TheSoundCoder/GameChatBalancer/AudioControl/Resources/Chat.png

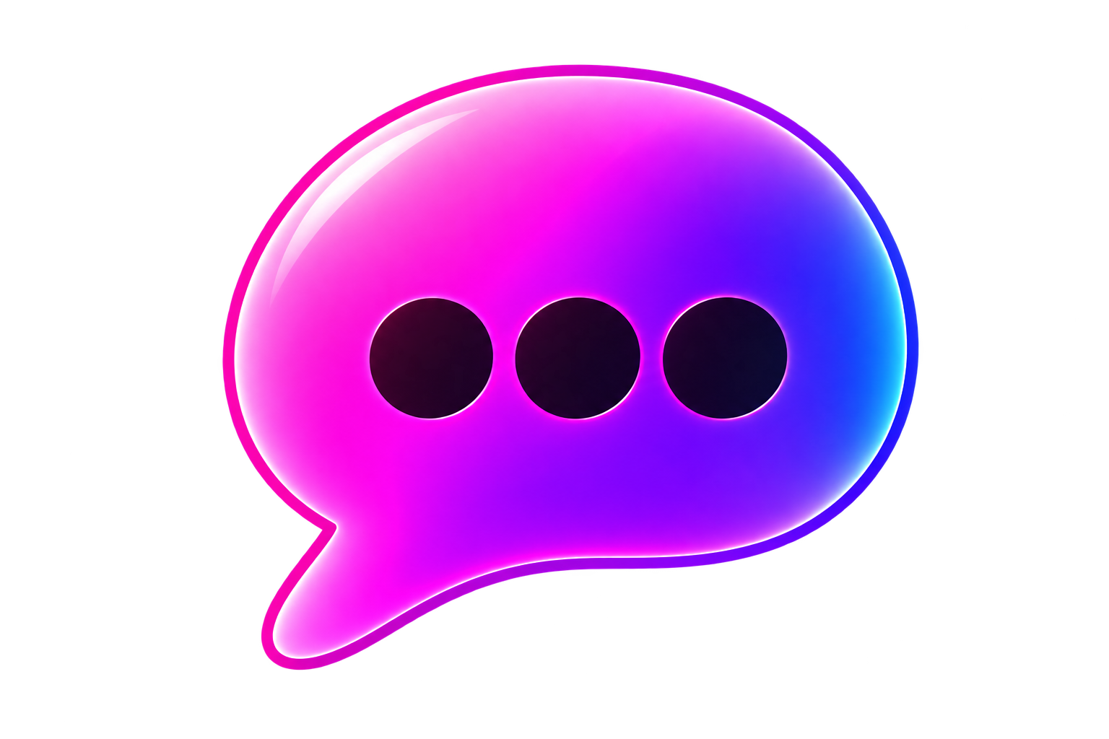
AudioControl/Resources/Chat.png
