TheSoundCoder/GameChatBalancer/AudioControl/Resources/Gamepad.png

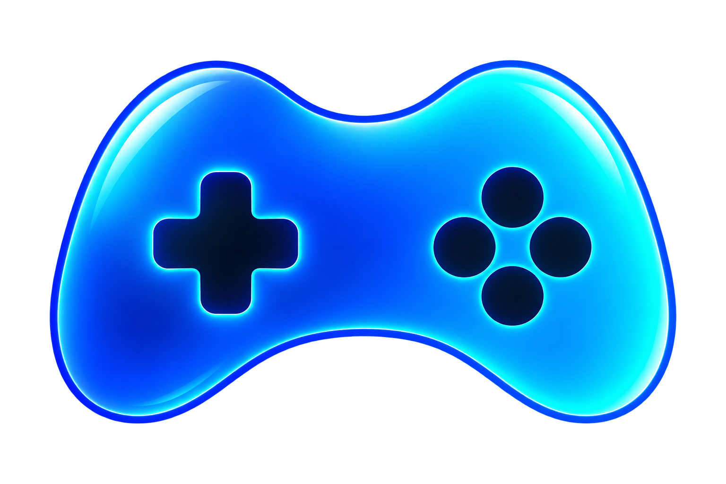
AudioControl/Resources/Gamepad.png
