TheSoundCoder/GameChatBalancer/AudioControl/Resources/ico_game2.png

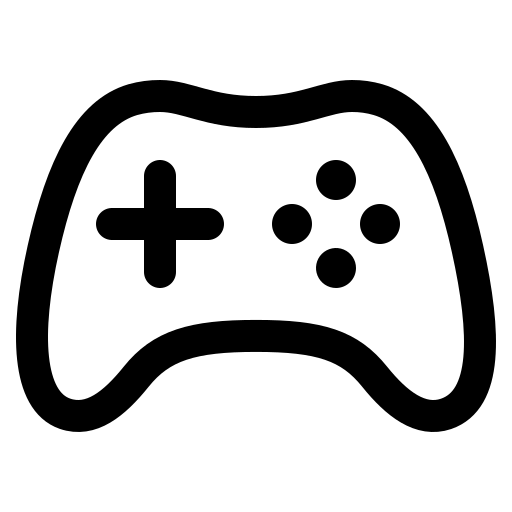
AudioControl/Resources/ico_game2.png
