TheSoundCoder/GameChatBalancer/AudioControl/Resources/Title_Background.png

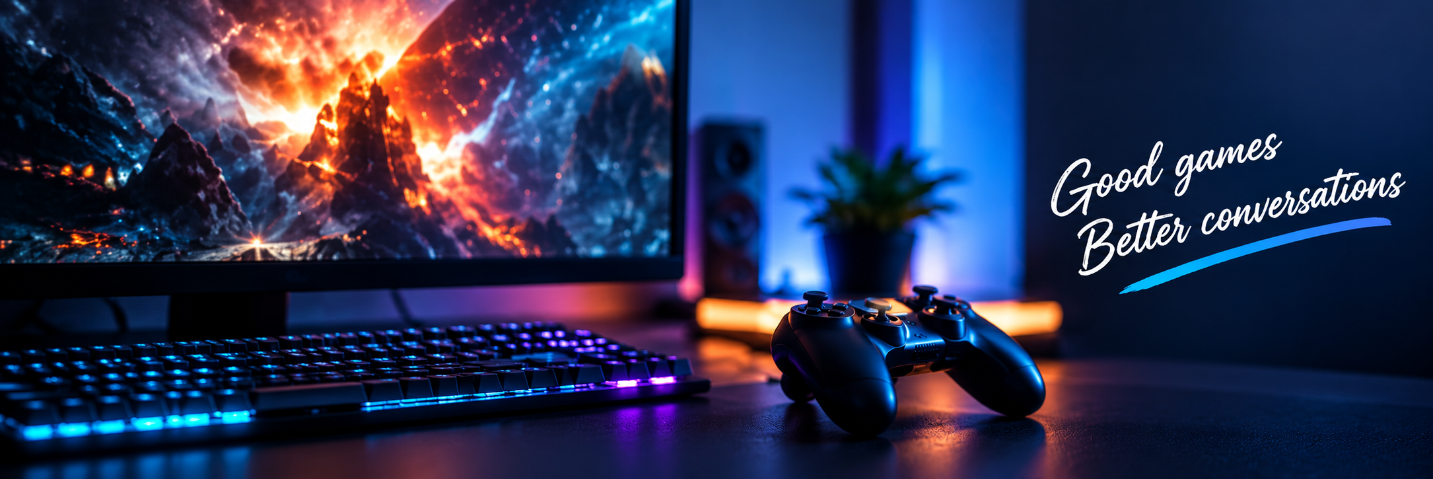
AudioControl/Resources/Title_Background.png
